draklowell/Cpu8/periphery/test_19_jan/interface_10.csv

time | not_read | not_write | address | data | clk
676 | 1 | 1 | 64962 | 0 | 0
1612 | 1 | 1 | 64962 | 0 | 0
2596 | 1 | 1 | 64962 | 0 | 0
3584 | 1 | 1 | 64962 | 0 | 0
5164 | 1 | 1 | 64962 | 0 | 0
6856 | 1 | 1 | 64962 | 0 | 0
8556 | 1 | 1 | 64962 | 0 | 0
10264 | 1 | 1 | 64962 | 0 | 0
12044 | 1 | 1 | 64962 | 0 | 0
13828 | 1 | 1 | 64962 | 0 | 0
15612 | 1 | 1 | 64962 | 0 | 0
17396 | 1 | 1 | 64962 | 0 | 0
19184 | 1 | 1 | 64962 | 0 | 0
20968 | 1 | 1 | 64962 | 0 | 0
22760 | 1 | 1 | 64962 | 0 | 0
24536 | 1 | 1 | 64962 | 0 | 0
26324 | 1 | 1 | 64962 | 0 | 0
28108 | 1 | 1 | 64962 | 0 | 0
29900 | 1 | 1 | 64962 | 0 | 0
31680 | 1 | 1 | 64962 | 0 | 0
33464 | 1 | 1 | 64962 | 0 | 0
35248 | 1 | 1 | 64962 | 0 | 0
37040 | 1 | 1 | 64962 | 0 | 0
38816 | 1 | 1 | 64962 | 0 | 0
40604 | 1 | 1 | 64962 | 0 | 0
42388 | 1 | 1 | 64962 | 0 | 0
44180 | 1 | 1 | 64962 | 0 | 0
45956 | 1 | 1 | 64962 | 0 | 0
47744 | 1 | 1 | 64962 | 0 | 0
49528 | 1 | 1 | 64962 | 0 | 0
51320 | 1 | 1 | 64962 | 0 | 0
53096 | 1 | 1 | 64962 | 0 | 0
54884 | 1 | 1 | 64962 | 0 | 0
56668 | 1 | 1 | 64962 | 0 | 0
58460 | 1 | 1 | 64962 | 0 | 0
60240 | 1 | 1 | 64962 | 0 | 0
62024 | 1 | 1 | 64962 | 0 | 0
63808 | 1 | 1 | 64962 | 0 | 0
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
