draklowell/Cpu8/periphery/test_19_jan/interface_12.csv

time | not_read | not_write | address | data | clk
676 | 0 | 1 | 129 | 0 | 0
1512 | 0 | 1 | 129 | 0 | 0
2400 | 0 | 1 | 129 | 0 | 0
3280 | 0 | 1 | 129 | 0 | 0
4476 | 0 | 1 | 129 | 0 | 0
6008 | 0 | 1 | 129 | 0 | 0
7536 | 0 | 1 | 129 | 0 | 0
9068 | 0 | 1 | 129 | 0 | 0
10596 | 0 | 1 | 129 | 0 | 0
12212 | 0 | 1 | 129 | 0 | 0
13828 | 0 | 1 | 129 | 0 | 0
15448 | 0 | 1 | 129 | 0 | 0
17056 | 0 | 1 | 129 | 0 | 0
18672 | 0 | 1 | 129 | 0 | 0
20288 | 0 | 1 | 129 | 0 | 0
21904 | 0 | 1 | 129 | 0 | 0
23516 | 0 | 1 | 129 | 0 | 0
25132 | 0 | 1 | 129 | 0 | 0
26756 | 0 | 1 | 129 | 0 | 0
28364 | 0 | 1 | 129 | 0 | 0
29976 | 0 | 1 | 129 | 0 | 0
31592 | 0 | 1 | 129 | 0 | 0
33208 | 0 | 1 | 129 | 0 | 0
34828 | 0 | 1 | 129 | 0 | 0
36436 | 0 | 1 | 129 | 0 | 0
38060 | 0 | 1 | 129 | 0 | 0
39668 | 0 | 1 | 129 | 0 | 0
41284 | 0 | 1 | 129 | 0 | 0
42896 | 0 | 1 | 129 | 0 | 0
44512 | 0 | 1 | 129 | 0 | 0
46132 | 0 | 1 | 129 | 0 | 0
47744 | 0 | 1 | 129 | 0 | 0
49364 | 0 | 1 | 129 | 0 | 0
50972 | 0 | 1 | 129 | 0 | 0
52588 | 0 | 1 | 129 | 0 | 0
54204 | 0 | 1 | 129 | 0 | 0
55816 | 0 | 1 | 129 | 0 | 0
57440 | 0 | 1 | 129 | 0 | 0
59048 | 0 | 1 | 129 | 0 | 0
60664 | 0 | 1 | 129 | 0 | 0
62276 | 0 | 1 | 129 | 0 | 0
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
