draklowell/Cpu8/periphery/test_19_jan/interface_2.csv

time | not_read | not_write | address | data | clk
676 | 1 | 1 | 0 | 0 | 0
1416 | 1 | 1 | 0 | 0 | 0
2200 | 1 | 1 | 0 | 0 | 0
2984 | 1 | 1 | 0 | 0 | 0
3800 | 1 | 1 | 0 | 0 | 0
5164 | 1 | 1 | 0 | 0 | 0
6516 | 1 | 1 | 0 | 0 | 0
7880 | 1 | 1 | 0 | 0 | 0
9244 | 1 | 1 | 0 | 0 | 0
10600 | 1 | 1 | 0 | 0 | 0
12044 | 1 | 1 | 0 | 232 | 0
13660 | 1 | 1 | 0 | 248 | 0
15272 | 1 | 1 | 0 | 254 | 0
16888 | 1 | 1 | 0 | 254 | 0
18508 | 1 | 1 | 0 | 254 | 0
20120 | 1 | 1 | 0 | 0 | 0
21568 | 1 | 1 | 0 | 0 | 0
23008 | 1 | 1 | 0 | 0 | 0
24452 | 1 | 1 | 0 | 0 | 0
25900 | 1 | 1 | 0 | 0 | 0
27344 | 1 | 1 | 0 | 0 | 0
28796 | 1 | 1 | 0 | 0 | 0
30232 | 1 | 1 | 0 | 0 | 0
31680 | 1 | 1 | 0 | 232 | 0
33292 | 1 | 1 | 0 | 248 | 0
34912 | 1 | 1 | 0 | 254 | 0
36524 | 1 | 1 | 0 | 254 | 0
38136 | 1 | 1 | 0 | 254 | 0
39752 | 1 | 1 | 0 | 32 | 0
41284 | 1 | 1 | 0 | 0 | 0
42728 | 1 | 1 | 0 | 0 | 0
44180 | 1 | 1 | 0 | 0 | 0
45620 | 1 | 1 | 0 | 0 | 0
47064 | 1 | 1 | 0 | 0 | 0
48508 | 1 | 1 | 0 | 0 | 0
49952 | 1 | 1 | 0 | 0 | 0
51404 | 1 | 1 | 0 | 232 | 0
53012 | 1 | 1 | 0 | 248 | 0
54628 | 1 | 1 | 0 | 254 | 0
56244 | 1 | 1 | 0 | 254 | 0
57860 | 1 | 1 | 0 | 254 | 0
59480 | 1 | 1 | 0 | 32 | 0
61004 | 1 | 1 | 0 | 0 | 0
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
