draklowell/Cpu8/periphery/tests_16_jan/test_4/interface_1.csv

time | not_read | not_write | address | data | clk
676 | 1 | 1 | 0 | 4 | 0
1416 | 1 | 1 | 0 | 4 | 0
2200 | 1 | 1 | 0 | 4 | 0
2984 | 1 | 1 | 0 | 4 | 0
3800 | 1 | 1 | 0 | 4 | 0
5164 | 1 | 1 | 0 | 4 | 0
6516 | 1 | 1 | 0 | 4 | 0
7880 | 1 | 1 | 0 | 4 | 0
9244 | 1 | 1 | 0 | 4 | 0
10600 | 1 | 1 | 0 | 4 | 0
12044 | 1 | 1 | 0 | 4 | 0
13496 | 1 | 1 | 0 | 4 | 0
14932 | 1 | 1 | 0 | 4 | 0
16380 | 1 | 1 | 0 | 4 | 0
17824 | 1 | 1 | 0 | 4 | 0
19268 | 1 | 1 | 0 | 4 | 0
20712 | 1 | 1 | 0 | 4 | 0
22156 | 1 | 1 | 0 | 4 | 0
23608 | 1 | 1 | 0 | 4 | 0
25048 | 1 | 1 | 0 | 4 | 0
26492 | 1 | 1 | 0 | 4 | 0
27936 | 1 | 1 | 0 | 4 | 0
29384 | 1 | 1 | 0 | 4 | 0
30836 | 1 | 1 | 0 | 4 | 0
32272 | 1 | 1 | 0 | 4 | 0
33716 | 1 | 1 | 0 | 4 | 0
35164 | 1 | 1 | 0 | 4 | 0
36608 | 1 | 1 | 0 | 4 | 0
38060 | 1 | 1 | 0 | 4 | 0
39496 | 1 | 1 | 0 | 4 | 0
40944 | 1 | 1 | 0 | 4 | 0
42388 | 1 | 1 | 0 | 4 | 0
43832 | 1 | 1 | 0 | 4 | 0
45284 | 1 | 1 | 0 | 4 | 0
46724 | 1 | 1 | 0 | 4 | 0
48176 | 1 | 1 | 0 | 4 | 0
49612 | 1 | 1 | 0 | 4 | 0
51060 | 1 | 1 | 0 | 4 | 0
52504 | 1 | 1 | 0 | 4 | 0
53948 | 1 | 1 | 0 | 4 | 0
55400 | 1 | 1 | 0 | 4 | 0
56840 | 1 | 1 | 0 | 4 | 0
58284 | 1 | 1 | 0 | 4 | 0
59728 | 1 | 1 | 0 | 4 | 0
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
